TheRepairforge/PocketOBI/strings_i18n.h

#pragma once
// i18n string data extracted from PocketOBI.ino.
// Data only: the Lang/StrId enums, the language codes, and the string table. The
// tr() accessor and the mutable `lang` selector are logic/state and stay in the sketch.
// `const` gives these internal linkage, so a header definition is safe (single TU today,
// no ODR clash if a future split includes it in several).

// ---------- i18n (string table; GFX fonts are ASCII-only, so no accents:
// FR/ES accents dropped, German umlauts as ae/oe/ue/ss) ----------
// LANG_COUNT = the four columns of STRTAB below. Japanese (D19) is NOT a STRTAB column:
// its strings live in strings_ja.h and only exist when ENABLE_CJK=1, so this table stays
// four-wide for PackScope/tools/gen_locales.py. Use LANG_NUM (cjk_render.h) for "how many
// languages can the user select".
enum Lang { LANG_EN, LANG_FR, LANG_DE, LANG_ES, LANG_COUNT, LANG_JA = LANG_COUNT };
const char* const LANG_CODE[LANG_COUNT] = { "EN", "FR", "DE", "ES" };

enum StrId {
  S_BATTERY, S_REPAIR, S_TOOLS, S_ABOUT,                       // launcher (order = tiles)
  S_PC_BRIDGE, S_LEDS_ON, S_LEDS_OFF, S_RESET_ERROR, S_DEBUG_RAW, S_SETTINGS, // tools (order)
  S_FLIP, S_BRIDGE_BOOT, S_LANGUAGE,                           // settings (order)
  S_HEALTHY, S_UNLOCK, S_HARDWARE_FIX, S_SUSPECT_HW, S_NO_PACK, // verdict
  S_HDR_HEALTH, S_HDR_IDENTITY,                                // headers
  // Battery Overview + Health + Identity labels
  S_PACK, S_TEMP, S_SPREAD, S_CHARGES,
  S_CONDITION, S_OVERDISCHARGE, S_OVERLOAD, S_CELLS, S_LATCHED,
  S_MODEL, S_SN, S_CAPACITY, S_TYPE, S_PRODUCED, S_ASSEMBLED, S_NUM_CHARGES, S_DATES_NOTE,
  // Repair diag rows + values + prediction + hint
  S_CHARGER_LOCK, S_LATCHED_FAULT, S_THERMISTOR, S_CELL_BALANCE,
  S_NONE, S_YES, S_OKV, S_FAULTV, S_BADV,
  S_WILL_HOLD, S_WONT_HOLD, S_NOT_LOCKED, S_HINT_CONT_CANCEL, S_FRAME_VALID_NOTHING,
  // Repair confirm / result
  S_NOT_SUPPORTED, S_HINT_CLICK_TURN_BACK, S_FRAME_ALREADY_VALID, S_NOTHING_NO_WRITE,
  S_WARN_WRITES_FLASH, S_REPAIRS_FALSE_ONLY, S_CLICK_WRITE, S_TURN_CANCEL,
  S_BEFORE, S_AFTER, S_NO_READ_AFTER, S_UNLOCKED_RES, S_STILL_LOCKED, S_RETRY_REINSERT,
  // Reset
  S_RESET_ERROR_Q, S_CMD_SENT, S_CLICK_CONFIRM, S_RESET_DONE,
  S_ERR_CLEARED, S_UNCHANGED, S_STATE_ARROW, S_LOCKEDV, S_OKSTATE, S_NO_ERROR,
  // PC bridge
  S_PC_MODE, S_BRIDGE_ACTIVE, S_BRIDGE_INACTIVE, S_PC_HELP1, S_PC_HELP2, S_PC_HELP3,
  S_HINT_TURN_TOGGLE_EXIT,
  // About / comm error / toasts / common hints
  S_SCAN, S_HINT_CLICK_BACK, S_HINT_CLICK_BACK_P, S_COMM_ERROR_HDR,
  S_NO_RESPONSE, S_CHECK_DATA, S_CHECK_PULLUPS, S_LEDS_ON_MSG, S_LEDS_OFF_MSG, S_HINT_TOGGLE_SAVE,
  // Repair diagnostic engine (wizard)
  S_CANNOT_DIAG, S_NO_PACK_REPLY1, S_NO_PACK_REPLY2, S_NO_DIAGNOSIS,
  S_HW_SENSE, S_HW_WEAK, S_HW_IMB, S_HW_THERM,
  S_ACT_SENSE, S_ACT_WEAK, S_ACT_IMB, S_ACT_THERM,
  S_FIX_HW_FIRST, S_UNLIKELY_HOLD, S_SHOULD_HOLD,
  S_NO_LOCK_NO_FAULT, S_BMS_MEMORISED, S_FALSE_LOCKOUT,
  S_PACK_HEALTHY, S_WHY_OD, S_WHY_OL, S_WHY_WEAR, S_WHY_UNCLEAR, S_WHY_THERM_CHECK, S_UNLOCK_SHOULD_HOLD,
  S_HINT_CONTINUE_BACK, S_HINT_FIXHW_BACK, S_HINT_NOTHING_BACK,
  S_TOAST_FIXHW, S_TOAST_NOTHING, S_WORKING, S_FRAME_STORE_PC,
  S_HINT_TAG,
  S_TEMP_CB,   // "Cell/Board" temp-row label (Temp1=cell, Temp2=board)
  S_CALIBRATE, // Settings > Calibrate touch (CYD touch board only)
  S_CAL_TAP, S_CAL_SAVED,  // touch calibration screen (CYD only)
  S_COUNT
};
const char* const STRTAB[S_COUNT][LANG_COUNT] = {
  //                  EN                 FR                 DE                   ES
  /*S_BATTERY*/     { "Battery",         "Batterie",        "Akku",              "Bateria" },
  /*S_REPAIR*/      { "Repair",          "Reparer",         "Reparatur",         "Reparar" },
  /*S_TOOLS*/       { "Tools",           "Outils",          "Werkzeuge",         "Utiles" },
  /*S_ABOUT*/       { "About",           "A propos",        "Info",              "Acerca" },
  /*S_PC_BRIDGE*/   { "PC bridge",       "Pont PC",         "PC-Bruecke",        "Puente PC" },
  /*S_LEDS_ON*/     { "Pack LEDs on",    "LEDs pack ON",    "Akku-LEDs an",      "LEDs bat. ON" },
  /*S_LEDS_OFF*/    { "Pack LEDs off",   "LEDs pack OFF",   "Akku-LEDs aus",     "LEDs bat. OFF" },
  /*S_RESET_ERROR*/ { "Reset error",     "Reset erreur",    "Fehler-Reset",      "Reset error" },
  /*S_DEBUG_RAW*/   { "Debug / raw",     "Debug / brut",    "Debug / roh",       "Debug / bruto" },
  /*S_SETTINGS*/    { "Settings",        "Reglages",        "Einstellungen",     "Ajustes" },
  /*S_FLIP*/        { "Flip screen",     "Ecran inverse",   "Bild drehen",       "Girar pantalla" },
  /*S_BRIDGE_BOOT*/ { "PC bridge at boot","Pont PC au boot","PC-Bruecke b.Start","Puente al inicio" },
  /*S_LANGUAGE*/    { "Language",        "Langue",          "Sprache",           "Idioma" },
  /*S_HEALTHY*/     { "HEALTHY",         "SAINE",           "GESUND",            "SANA" },
  /*S_UNLOCK*/      { "UNLOCK",          "DEBLOQUER",       "ENTSPERREN",        "DESBLOQUEAR" },
  /*S_HARDWARE_FIX*/{ "HARDWARE FIX",    "REPA MATERIEL",   "HARDWARE-REP.",     "REP. HARDWARE" },
  /*S_SUSPECT_HW*/  { "POSSIBLE HW FIX", "REPA MAT. POSS.", "EVTL. HARDWARE",    "POSIBLE REP." },
  /*S_NO_PACK*/     { "NO PACK",         "PAS DE PACK",     "KEIN AKKU",         "SIN BATERIA" },
  /*S_HDR_HEALTH*/  { "Health",          "Sante",           "Zustand",           "Salud" },
  /*S_HDR_IDENTITY*/{ "Identity",        "Identite",        "Identitaet",        "Identidad" },
  /*S_PACK*/        { "PACK",            "PACK",             "PACK",              "PACK" },
  /*S_TEMP*/        { "Temp",            "Temp",             "Temp",              "Temp" },
  /*S_SPREAD*/      { "Spread",          "Ecart",            "Diff.",             "Dif." },
  /*S_CHARGES*/     { "Charges",         "Charges",          "Zyklen",            "Cargas" },
  /*S_CONDITION*/   { "Condition",       "Etat",             "Zustand",           "Estado" },
  /*S_OVERDISCHARGE*/{ "Over-discharge", "Sur-decharge",     "Tiefentladung",     "Sobredescarga" },
  /*S_OVERLOAD*/    { "Over-load",       "Surcharge",        "Ueberlast",         "Sobrecarga" },
  /*S_CELLS*/       { "Cells",           "Cellules",         "Zellen",            "Celdas" },
  /*S_LATCHED*/     { "Latched",         "Verrou dur",       "Verriegelt",        "Bloqueo fijo" },
  /*S_MODEL*/       { "Model",           "Modele",           "Modell",            "Modelo" },
  /*S_SN*/          { "S/N",             "S/N",              "S/N",               "S/N" },
  /*S_CAPACITY*/    { "Capacity",        "Capacite",         "Kapazitaet",        "Capacidad" },
  /*S_TYPE*/        { "Type",            "Type",             "Typ",               "Tipo" },
  /*S_PRODUCED*/    { "Produced",        "Fabrique",         "Hergestellt",       "Fabricado" },
  /*S_ASSEMBLED*/   { "Assembled",       "Assemble",         "Montiert",          "Ensamblado" },
  /*S_NUM_CHARGES*/ { "Number of charges","Nombre de charges","Anzahl Ladungen",  "Numero de cargas" },
  /*S_DATES_NOTE*/  { "dates: YYYY-MM-DD","dates: AAAA-MM-JJ","Datum: JJJJ-MM-TT", "fechas: AAAA-MM-DD" },
  /*S_CHARGER_LOCK*/{ "Charger lock",    "Verrou chargeur",  "Ladesperre",        "Bloqueo carga" },
  /*S_LATCHED_FAULT*/{ "Latched fault",  "Defaut latche",    "Fehler fix",        "Fallo fijo" },
  /*S_THERMISTOR*/  { "Thermistor",      "Thermistance",     "Thermistor",        "Termistor" },
  /*S_CELL_BALANCE*/{ "Cell balance",    "Equilibre cell",   "Zellbalance",       "Balance celda" },
  /*S_NONE*/        { "none",            "aucun",            "keine",             "ninguno" },
  /*S_YES*/         { "yes",             "oui",              "ja",                "si" },
  /*S_OKV*/         { "ok",              "ok",               "ok",                "ok" },
  /*S_FAULTV*/      { "fault",           "defaut",           "Fehler",            "fallo" },
  /*S_BADV*/        { "bad",             "mauvais",          "schlecht",          "malo" },
  /*S_WILL_HOLD*/   { "WILL HOLD",       "VA TENIR",         "HAELT",             "AGUANTA" },
  /*S_WONT_HOLD*/   { "WON'T HOLD",      "NE TIENDRA PAS",   "HAELT NICHT",       "NO AGUANTA" },
  /*S_NOT_LOCKED*/  { "NOT LOCKED",      "NON VERROUILLE",   "NICHT GESPERRT",    "NO BLOQUEADO" },
  /*S_HINT_CONT_CANCEL*/{ "Click = continue    Turn = cancel","Clic = continuer   Tour = annuler","Klick = weiter   Drehen = abbr.","Clic = seguir   Giro = cancelar" },
  /*S_FRAME_VALID_NOTHING*/{ "Frame valid - nothing to repair","Trame valide - rien a reparer","Frame ok - nichts zu tun","Trama ok - nada que reparar" },
  /*S_NOT_SUPPORTED*/{ "F0513: not supported","F0513: non supporte","F0513: nicht unterst.","F0513: no soportado" },
  /*S_HINT_CLICK_TURN_BACK*/{ "(click / turn = back)","(clic / tour = retour)","(Klick/Drehen=zurueck)","(clic/giro = atras)" },
  /*S_FRAME_ALREADY_VALID*/{ "Frame already valid.","Trame deja valide.","Frame schon gueltig.","Trama ya valida." },
  /*S_NOTHING_NO_WRITE*/{ "Nothing to repair - no write done.","Rien a reparer - aucune ecriture.","Nichts zu tun - kein Schreiben.","Nada que reparar - sin escritura." },
  /*S_WARN_WRITES_FLASH*/{ "WARNING: writes to the BMS flash.","ATTENTION: ecrit la flash du BMS.","WARNUNG: schreibt BMS-Flash.","AVISO: escribe flash del BMS." },
  /*S_REPAIRS_FALSE_ONLY*/{ "Repairs a false lockout only.","Repare un faux verrou seulement.","Nur Fehlsperre reparieren.","Solo repara bloqueo falso." },
  /*S_CLICK_WRITE*/ { "Click = write",   "Clic = ecrire",    "Klick = schreiben", "Clic = escribir" },
  /*S_TURN_CANCEL*/ { "Turn  = cancel",  "Tour  = annuler",  "Drehen = abbrechen","Giro  = cancelar" },
  /*S_BEFORE*/      { "Before",          "Avant",            "Vorher",            "Antes" },
  /*S_AFTER*/       { "After",           "Apres",            "Nachher",           "Despues" },
  /*S_NO_READ_AFTER*/{ "-> No read after write","-> Pas de lecture apres","-> Kein Lesen danach","-> Sin lectura despues" },
  /*S_UNLOCKED_RES*/{ "-> Unlocked!",    "-> Deverrouille!", "-> Entsperrt!",     "-> Desbloqueado!" },
  /*S_STILL_LOCKED*/{ "-> Still locked", "-> Toujours verrou","-> Noch gesperrt", "-> Aun bloqueado" },
  /*S_RETRY_REINSERT*/{ "To retry, remove & reinsert the pack.","Pour reessayer, retire et remets le pack.","Zum Wiederholen Akku neu einsetzen.","Reintentar: reinserta la bateria." },
  /*S_RESET_ERROR_Q*/{ "RESET ERROR?",   "RESET ERREUR?",    "FEHLER RESET?",     "RESET ERROR?" },
  /*S_CMD_SENT*/    { "Command sent:",   "Commande envoyee:","Befehl gesendet:",  "Comando enviado:" },
  /*S_CLICK_CONFIRM*/{ "Click = confirm","Clic = confirmer", "Klick = bestaetig.","Clic = confirmar" },
  /*S_RESET_DONE*/  { "RESET DONE",      "RESET FAIT",       "RESET FERTIG",      "RESET HECHO" },
  /*S_ERR_CLEARED*/ { "-> Error cleared!","-> Erreur effacee!","-> Fehler geloescht!","-> Error borrado!" },
  /*S_UNCHANGED*/   { "-> Unchanged",    "-> Inchange",      "-> Unveraendert",   "-> Sin cambio" },
  /*S_STATE_ARROW*/ { "-> State:",       "-> Etat:",         "-> Zustand:",       "-> Estado:" },
  /*S_LOCKEDV*/     { "LOCKED",          "VERROUILLE",       "GESPERRT",          "BLOQUEADO" },
  /*S_OKSTATE*/     { "OK",              "OK",               "OK",                "OK" },
  /*S_NO_ERROR*/    { "-> No error to clear","-> Aucune erreur a effacer","-> Kein Fehler","-> Sin error que borrar" },
  /*S_PC_MODE*/     { "PC MODE",         "MODE PC",          "PC-MODUS",          "MODO PC" },
  /*S_BRIDGE_ACTIVE*/{ "USB bridge ACTIVE","Pont USB ACTIF", "USB-Bruecke AKTIV", "Puente USB ACTIVO" },
  /*S_BRIDGE_INACTIVE*/{ "bridge INACTIVE","pont INACTIF",   "Bruecke INAKTIV",   "puente INACTIVO" },
  /*S_PC_HELP1*/    { "Open 'Open Battery Information' on","Ouvre 'Open Battery Information'","Oeffne 'Open Battery Information'","Abre 'Open Battery Information'" },
  /*S_PC_HELP2*/    { "your PC, pick the Arduino OBI","sur ton PC, choisis Arduino OBI","am PC, waehle Arduino OBI","en tu PC, elige Arduino OBI" },
  /*S_PC_HELP3*/    { "interface + this COM port.","interface + ce port COM.","Schnittstelle + COM-Port.","interfaz + este puerto COM." },
  /*S_HINT_TURN_TOGGLE_EXIT*/{ "(turn = toggle    back = exit)","(tour = bascule   retour = sortie)","(Drehen=um   zurueck=Ende)","(giro = alterna   atras = salir)" },
  /*S_SCAN*/        { "scan",            "scan",             "scan",              "escanea" },
  /*S_HINT_CLICK_BACK*/{ "click = back", "clic = retour",    "Klick = zurueck",   "clic = atras" },
  /*S_HINT_CLICK_BACK_P*/{ "(click = back)","(clic = retour)","(Klick = zurueck)","(clic = atras)" },
  /*S_COMM_ERROR_HDR*/{ "COMM ERROR",    "ERREUR COMM",      "COMM-FEHLER",       "ERROR COMM" },
  /*S_NO_RESPONSE*/ { "No response on bus.","Pas de reponse sur le bus.","Keine Antwort am Bus.","Sin respuesta en bus." },
  /*S_CHECK_DATA*/  { "Check DATA wiring,","Verifie le cablage DATA,","DATA-Verdrahtung pruefen,","Revisa cableado DATA," },
  /*S_CHECK_PULLUPS*/{ "pull-ups and GND.","pull-ups et GND.","Pull-ups und GND.","pull-ups y GND." },
  /*S_LEDS_ON_MSG*/ { "LEDs ON",         "LEDs ON",          "LEDs AN",           "LEDs ON" },
  /*S_LEDS_OFF_MSG*/{ "LEDs OFF",        "LEDs OFF",         "LEDs AUS",          "LEDs OFF" },
  /*S_HINT_TOGGLE_SAVE*/{ "click = toggle     back = save & exit","clic = changer   retour = sauver","Klick=um   zurueck=speichern","clic=cambia   atras=guardar" },
  /*S_CANNOT_DIAG*/ { "Cannot diagnose",  "Diagnostic impossible","Diagnose unmoeglich","No se puede diagnosticar" },
  /*S_NO_PACK_REPLY1*/{ "No pack reply. Check the adapter, the","Pas de reponse. Verifie l'adaptateur,","Keine Antwort. Adapter pruefen,","Sin respuesta. Revisa el adaptador," },
  /*S_NO_PACK_REPLY2*/{ "DATA/ENABLE wiring, or a dead BMS.","le cablage DATA/ENABLE, ou BMS mort.","DATA/ENABLE-Kabel, oder BMS tot.","cableado DATA/ENABLE, o BMS muerto." },
  /*S_NO_DIAGNOSIS*/{ "NO DIAGNOSIS",    "PAS DE DIAG",       "KEINE DIAGNOSE",    "SIN DIAGNOSTICO" },
  /*S_HW_SENSE*/    { "Broken sense wire","Fil de mesure casse","Sense-Draht defekt","Cable de sensado roto" },
  /*S_HW_WEAK*/     { "Weak / dead group","Groupe faible / mort","Gruppe schwach / tot","Grupo debil / muerto" },
  /*S_HW_IMB*/      { "Cell imbalance",   "Desequilibre cellules","Zellen unsymmetrisch","Desequilibrio celdas" },
  /*S_HW_THERM*/    { "Temp reading off", "Lecture temp anormale","Temp-Wert auffaellig","Lectura temp anomala" },
  /*S_ACT_SENSE*/   { "Resolder sense wire on group %d","Ressoude le fil du groupe %d","Sense-Draht Gruppe %d loeten","Resuelda sensor grupo %d" },
  /*S_ACT_WEAK*/    { "Measure group %d with a DMM","Mesure le groupe %d au multimetre","Gruppe %d mit DMM messen","Mide grupo %d con multimetro" },
  /*S_ACT_IMB*/     { "Group %d low: slow-charge, recheck","Groupe %d bas: charge lente, recontrole","Gruppe %d niedrig: langsam laden","Grupo %d bajo: carga lenta, revisa" },
  /*S_ACT_THERM*/   { "Re-read cold, then check NTC","Relire a froid, puis controler NTC","Kalt messen, dann NTC pruefen","Medir en frio, luego revisar NTC" },
  /*S_FIX_HW_FIRST*/{ "FIX HARDWARE FIRST","REPARER LE MATERIEL","ERST HARDWARE FIXEN","REPARA HARDWARE" },
  /*S_UNLIKELY_HOLD*/{ "UNLIKELY TO HOLD","PEU PROBABLE",      "HAELT WOHL NICHT",  "POCO PROBABLE" },
  /*S_SHOULD_HOLD*/ { "SHOULD HOLD",      "DEVRAIT TENIR",    "SOLLTE HALTEN",     "DEBERIA AGUANTAR" },
  /*S_NO_LOCK_NO_FAULT*/{ "No lock, no fault","Pas de verrou, pas de faute","Keine Sperre, kein Fehler","Sin bloqueo ni fallo" },
  /*S_BMS_MEMORISED*/{ "BMS memorised a fault","Le BMS a memorise une faute","BMS hat Fehler gespeichert","El BMS memorizo un fallo" },
  /*S_FALSE_LOCKOUT*/{ "False lockout",   "Faux verrouillage","Falsche Sperre",    "Bloqueo falso" },
  /*S_PACK_HEALTHY*/{ "Pack looks healthy.","Pack a l'air sain.","Akku wirkt gesund.","Bateria parece sana." },
  /*S_WHY_OD*/      { "Likely left flat (over-discharge).","Laisse a plat (sur-decharge).","Wohl tiefentladen.","Descargada del todo." },
  /*S_WHY_OL*/      { "Likely run in overload.","Utilise en surcharge.","Wohl ueberlastet.","Usada en sobrecarga." },
  /*S_WHY_WEAR*/    { "Consistent with normal wear.","Coherent avec usure normale.","Normaler Verschleiss.","Coherente con desgaste." },
  /*S_WHY_UNCLEAR*/ { "Cause unclear - see Health counters.","Cause floue - voir compteurs Sante.","Ursache unklar - Zustand pruefen.","Causa incierta - ver Salud." },
  /*S_WHY_THERM_CHECK*/{ "Cell/board temps differ - recheck","Temp cell/carte diverge - relire","Zell/Board-Temp weicht ab - neu","Temp celda/placa difiere - revisar" },
  /*S_UNLOCK_SHOULD_HOLD*/{ "Our unlock should hold.","Notre unlock devrait tenir.","Unser Entsperren sollte halten.","El desbloqueo deberia aguantar." },
  /*S_HINT_CONTINUE_BACK*/{ "Click = continue    Turn = back","Clic = continuer   Tour = retour","Klick = weiter   Drehen = zur.","Clic = seguir   Giro = atras" },
  /*S_HINT_FIXHW_BACK*/{ "Fix hardware first   Turn = back","Repare le materiel   Tour = retour","Erst Hardware fixen  Dreh=zur.","Repara hardware   Giro = atras" },
  /*S_HINT_NOTHING_BACK*/{ "Nothing to repair   Turn = back","Rien a reparer   Tour = retour","Nichts zu tun   Drehen = zur.","Nada que reparar   Giro = atras" },
  /*S_TOAST_FIXHW*/ { "Fix hardware first","Repare le materiel","Erst Hardware fixen","Repara hardware" },
  /*S_TOAST_NOTHING*/{ "Nothing to repair","Rien a reparer",   "Nichts zu reparieren","Nada que reparar" },
  /*S_WORKING*/     { "Working...",       "Travail...",       "Arbeite...",        "Trabajando..." },
  /*S_FRAME_STORE_PC*/{ "repair frame  ->  store  ->  power-cycle","repare -> stocke -> power-cycle","Frame -> speichern -> Neustart","repara -> guarda -> reinicio" },
  /*S_HINT_TAG*/    { "HINT",            "INDICE",           "HINWEIS",           "PISTA" },
  /*S_TEMP_CB*/     { "Cell/Board",      "Cell/Carte",       "Zelle/Platine",     "Celda/Placa" },
  /*S_CALIBRATE*/   { "Calibrate touch", "Calibrer tactile", "Touch kalibrieren", "Calibrar tactil" },
  /*S_CAL_TAP*/     { "Tap the target",  "Touchez la cible", "Ziel antippen",     "Toca el objetivo" },
  /*S_CAL_SAVED*/   { "Saved",           "Enregistre",       "Gespeichert",       "Guardado" },
};
